OasisOfChaos/hexawall/Images/20230205_133230.jpg

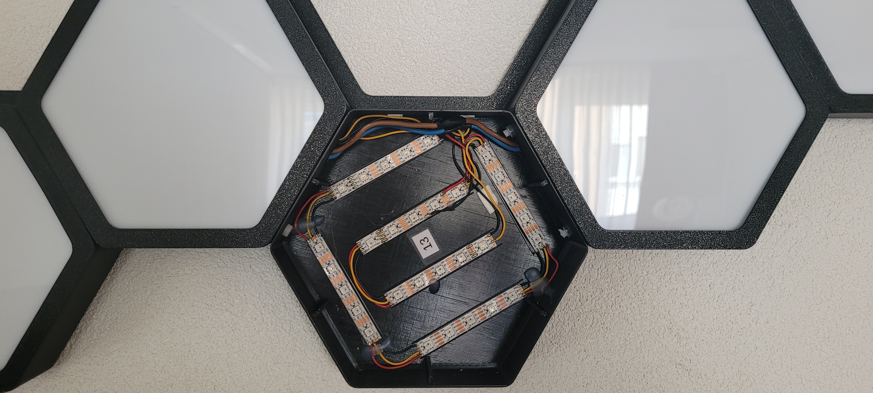
Images/20230205_133230.jpg
