OasisOfChaos/hexawall/Inventor/Flat Placeholder v1 - 175 - 12mm rim - A (3 flaps).stl

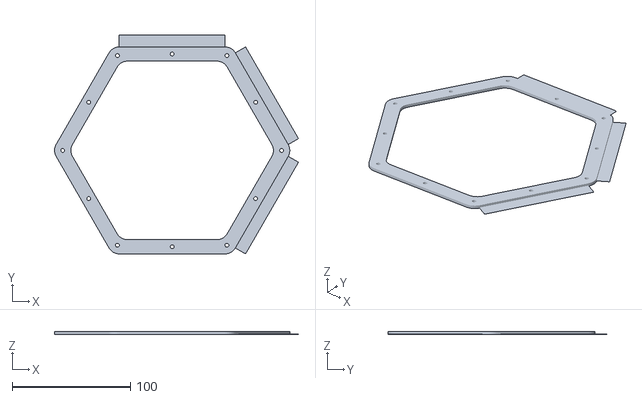
[picture p13: CAD file, 2023-02-05]
Inventor/Flat Placeholder v1 - 175 - 12mm rim - A (3 flaps).stl
206.3 x 185.0 x 2.50
