OasisOfChaos/hexawall/Inventor/Cover v2 - 175 - 12mm rim.stl

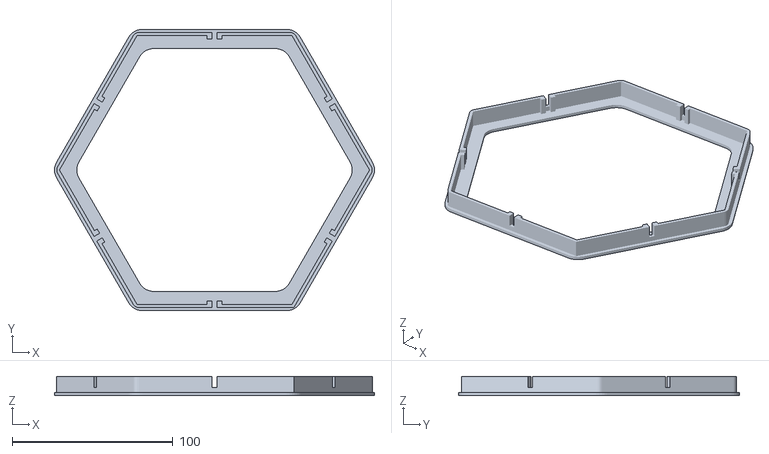
[picture p14: CAD file, 2023-02-05]
Inventor/Cover v2 - 175 - 12mm rim.stl
199.0 x 175.0 x 12.0
