OasisOfChaos/hexawall/Inventor/Cover v1 - 175 - 12mm rim - for thicker wall.stl

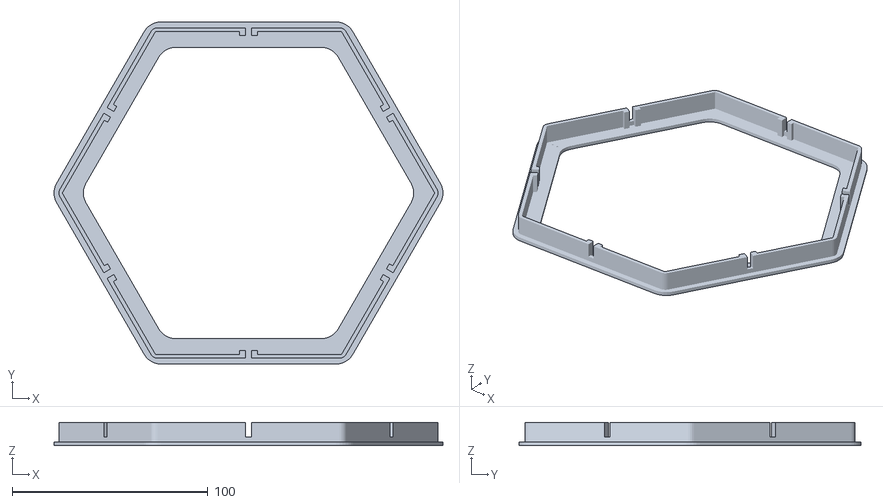
[picture p15: CAD file, 2023-02-05]
Inventor/Cover v1 - 175 - 12mm rim - for thicker wall.stl
199.0 x 175.0 x 12.0
