OasisOfChaos/hexawall/Inventor/Flat Placeholder v1 - 175 - 12mm rim - B.3mf

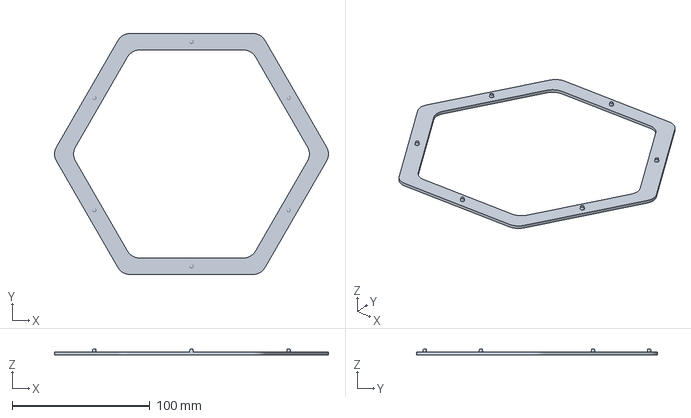
[picture p16: CAD file, 2023-02-05]
Inventor/Flat Placeholder v1 - 175 - 12mm rim - B.3mf
199.0 x 175.0 x 4.00 mm
