OasisOfChaos/hexawall/Inventor/Flat Placeholder v1 - 175 - 12mm rim - A.stl

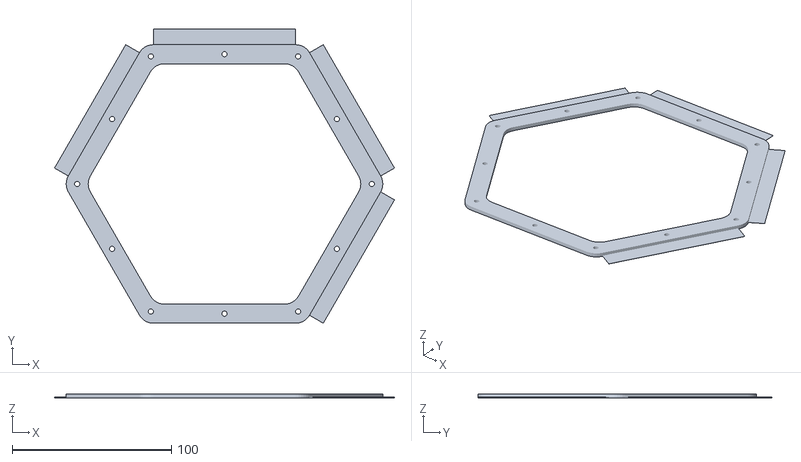
[picture p17: CAD file, 2023-02-05]
Inventor/Flat Placeholder v1 - 175 - 12mm rim - A.stl
213.6 x 185.0 x 2.50
