OasisOfChaos/hexawall/Inventor/Cover v1.stl

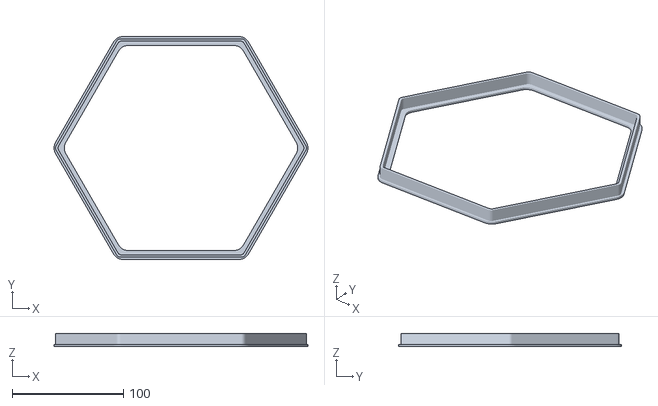
[picture p18: CAD file, 2023-02-05]
Inventor/Cover v1.stl
227.8 x 200.0 x 12.0
