OasisOfChaos/hexawall/Inventor/Aligner Helper v3.stl

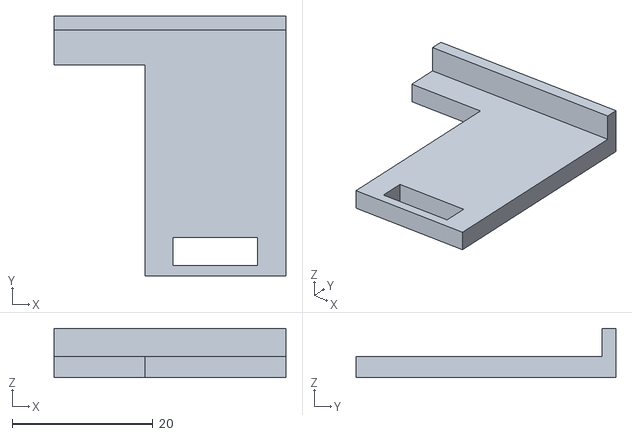
[picture p19: CAD file, 2023-02-05]
Inventor/Aligner Helper v3.stl
33.0 x 37.0 x 7.00
