OasisOfChaos/hexawall/Firmware/HexaWall/src/SequenceNames.hpp

#pragma once

#include "enum.h"

BETTER_ENUM(
	SequenceName,
	int,
	CyclePrimaryColors,
	CycleTertiaryColors,
	SolidColorBlend,
	SolidColorDirect,
	Pride,
	Dripping,
	TimedPalettes,
	Fire,
	Blendwave,
	Blur,
	Confetti,
	DotBeat,
	Easing,
	InoiseFire,
	Lightning,
	JugglePal,
	MatrixPal,
	Mover,
	FadeTest,
	FadeInLeftToRight,
	Noise16a,
	Noise16b,
	Noise16c,
	OneSinePal,
	PaletteCrossfade,
	Plasma,
	RainbowBeat,
	RainbowMarch,
	RipplePal,
	Ripples,
	//SawTooth,			//too boring
	//Serendipitous,	//too boring
	TwoSinPal,
	ThreeSinPal,
	SineLon,
	Breathing,
	//CandyCaneStripes,
	ChaseTargetValues,
	StripedPalettes,
	CylonColorChange,
	HeartPulseBloodFlow,
	//MovingColors,		//too boring
	SimulatedTVLighting,
	RepeatingBlockPattern,
	//RainbowBrightnessAndSaturation,		//too boring
	Pacifica,
	GradientPalette,
	//MovingGradient,	//sort out -- does not much now
	//Quadwave8FadeUp,	//sort out -- does not much now
	FireMirrored,
	//MirrorAndFadeEnds,
	ColumnTest,
	VertColumnLeftRight,

	None,
	SwitchOn,
	SwitchOff,
	//Cylon,			//bugs!
	NUM_ITEMS
);
