OasisOfChaos/hexawall/Firmware/HexaWall/src/sequences/SeqVertColumnLeftRight.hpp

// SeqVertColumnLeftRight.hpp
#pragma once

#include "arduino.h"
#include <FastLED.h>
#include "Sequence.hpp"

#define NUM_COLUMNS 11
#define NUM_ROWS 3

#define NUM_VERT_COLUMNS 10
#define NUM_VERT_ROWS 4

#define NUM_HORI_COLUMNS 4
#define NUM_HORI_ROWS 7

class SeqVertColumnLeftRight : public Sequence
{
private:
	uint8_t _sequence[NUM_COLUMNS][NUM_ROWS] = {
		{22, 21, 255},
		{23, 19, 255},
		{24, 20, 18},
		{14, 15, 16},
		{13, 17, 255},
		{11, 10, 9},
		{12, 8, 255},
		{3, 7, 255},
		{2, 4, 6},
		{1, 5, 255},
		{0, 255, 255}};

	uint8_t hexa_columns_vertical[NUM_VERT_COLUMNS][NUM_VERT_ROWS] = {
		{6, 255, 255, 255},
		{5, 8, 7, 255},	  //{5, 8, 255, 255},
		{4, 10, 25, 9},	  //{4, 10, 25, 255},
		{3, 24, 26, 255}, //{3, 24, 26, 11},
		{2, 11, 23, 27},
		{1, 12, 22, 28},
		{13, 21, 29, 255}, //{13, 21, 29, 1},
		{14, 20, 30, 19},  //{14, 20, 30, 255},
		{15, 18, 17, 255},
		{16, 255, 255, 255}};

	uint8_t _second = 0;

	int8_t _column = -1;
	bool _direction = true;

	CRGB _color;
	uint8_t _colorIndex = 0;

	CRGBPalette16 _currentPalette;
	TBlendType _currentBlending;

	void secondTick()
	{
		_second++;
	}

public:
	SeqVertColumnLeftRight(struct CRGB *data, int nLedsOrOffset) : Sequence(data, nLedsOrOffset)
	{
		_isFinished = false;

		_currentPalette = RainbowColors_p;
		//_currentPalette = ForestColors_p;
		_currentBlending = LINEARBLEND;
	}

	void tick()
	{
		EVERY_N_MILLISECONDS(30)
		{
			if (_isFinished)
			{
				return;
			}
			
			vertPaletteLeftToRight();

			FastLED.show();
		}
	}

	void vertPaletteLeftToRight()
	{

		for (uint8_t c = 0; c < NUM_COLUMNS; c++)
		{
			for (uint8_t r = 0; r < NUM_ROWS; r++)
			{
				if (_sequence[c][r] != 255)
				{
					int idx = this->getIndex(_sequence[c][r]);

					_color = ColorFromPalette(_currentPalette, _colorIndex, LEDBrightness, _currentBlending);

					for (uint8_t hc = 0; hc < NUM_VERT_COLUMNS; hc++)
					{
						for (uint8_t hr = 0; hr < NUM_VERT_ROWS; hr++)
						{
							int cvert = hexa_columns_vertical[hc][hr];
							if (cvert != 255)
							{
								LEDArray[idx + cvert] = _color;
								// Serial.printf("c: %d, r: %d, hc: %d, hr: %d, _sequence: %d, hexa_columns_vertical: %d\n", c, r, hc, hr, _sequence[c][r], cvert);
							}
						}

						_colorIndex += 1;
					}
				}
			}
		}
	}
};
